tjsauk/robot-dog/Paw pressure sensor files/20231229_134713.jpg

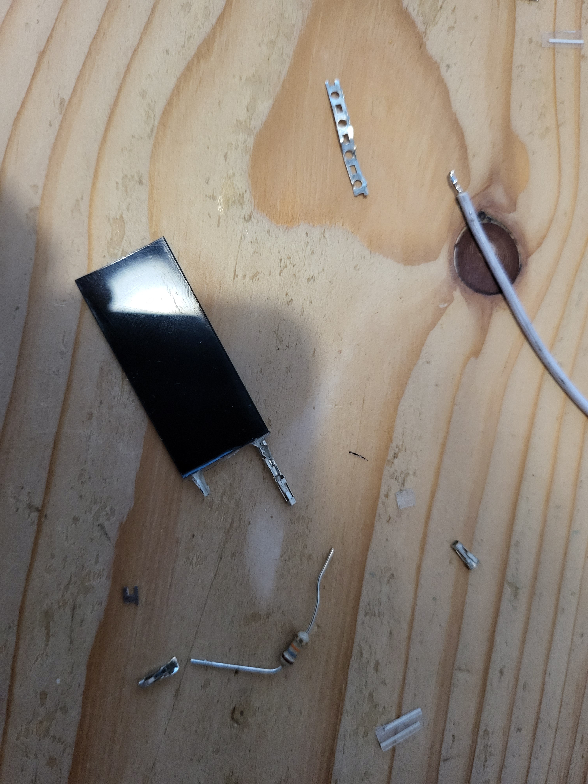
Paw pressure sensor files/20231229_134713.jpg
