tjsauk/robot-dog/Paw pressure sensor files/20231229_134718.jpg

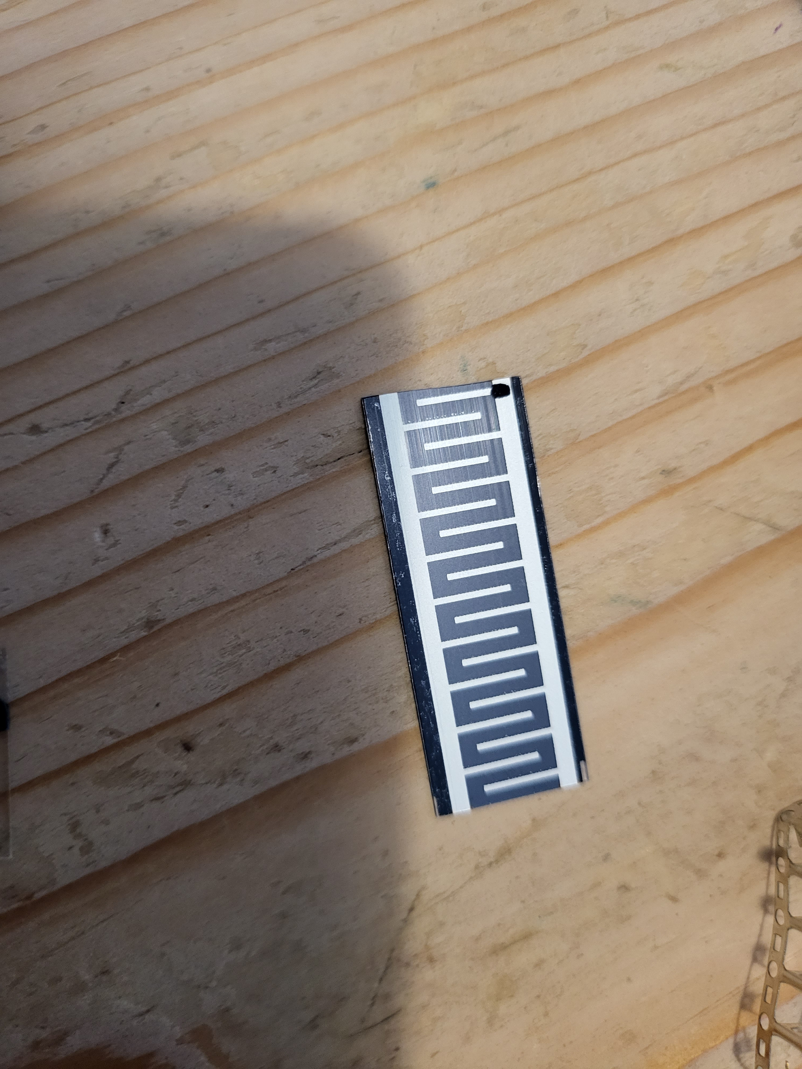
Paw pressure sensor files/20231229_134718.jpg
