tjsauk/robot-dog/Paw pressure sensor files/20231229_134710.jpg

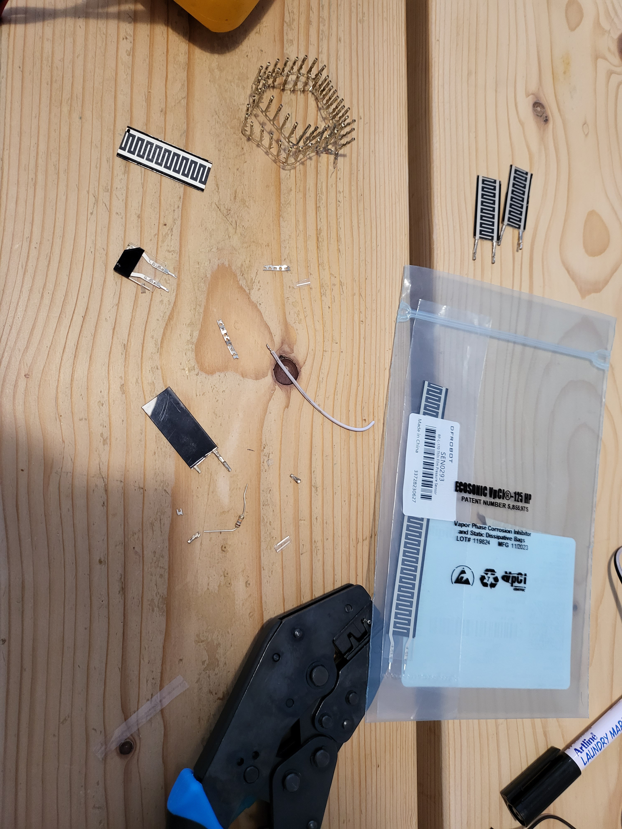
Paw pressure sensor files/20231229_134710.jpg
